zachmongare/Li-Fi-Communication-System/images/results/effective angle test.jpg

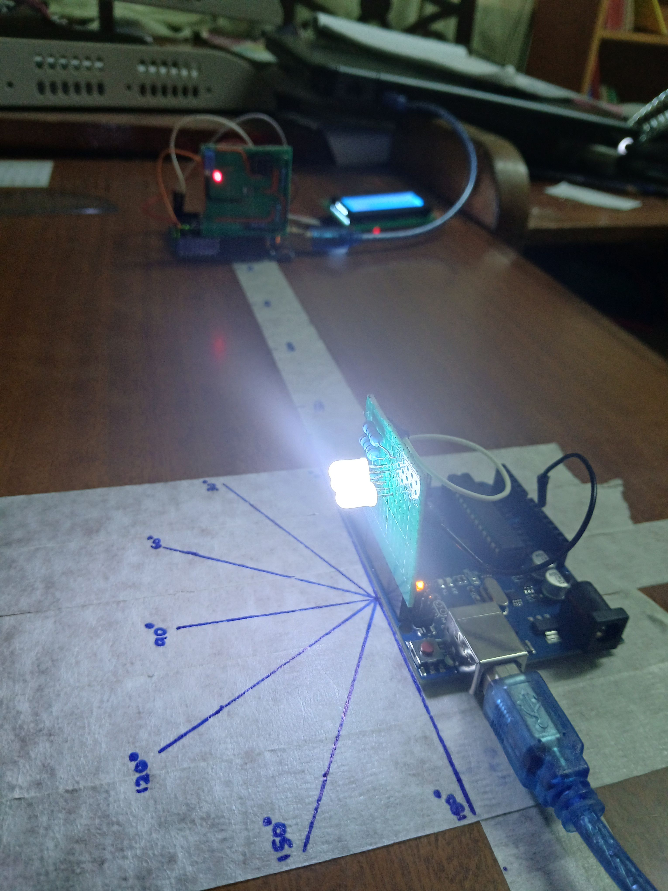
images/results/effective angle test.jpg
