zachmongare/Li-Fi-Communication-System/images/results/range and angle test.jpg

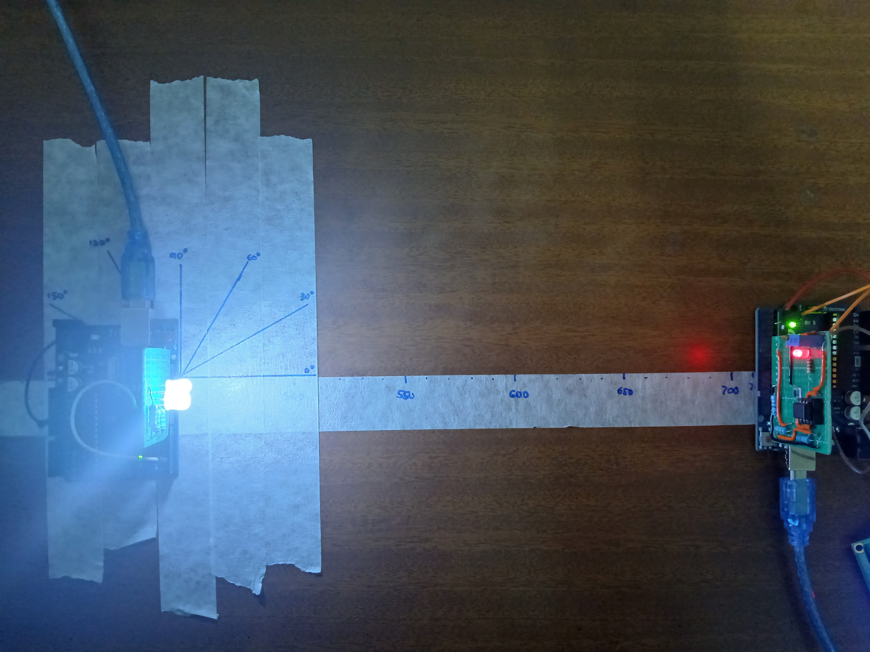
images/results/range and angle test.jpg
