zachmongare/Li-Fi-Communication-System/schematics/receiver_schematic.kicad_sch

## KiCad design schematics/receiver_schematic.kicad_sch (2025-07-15)

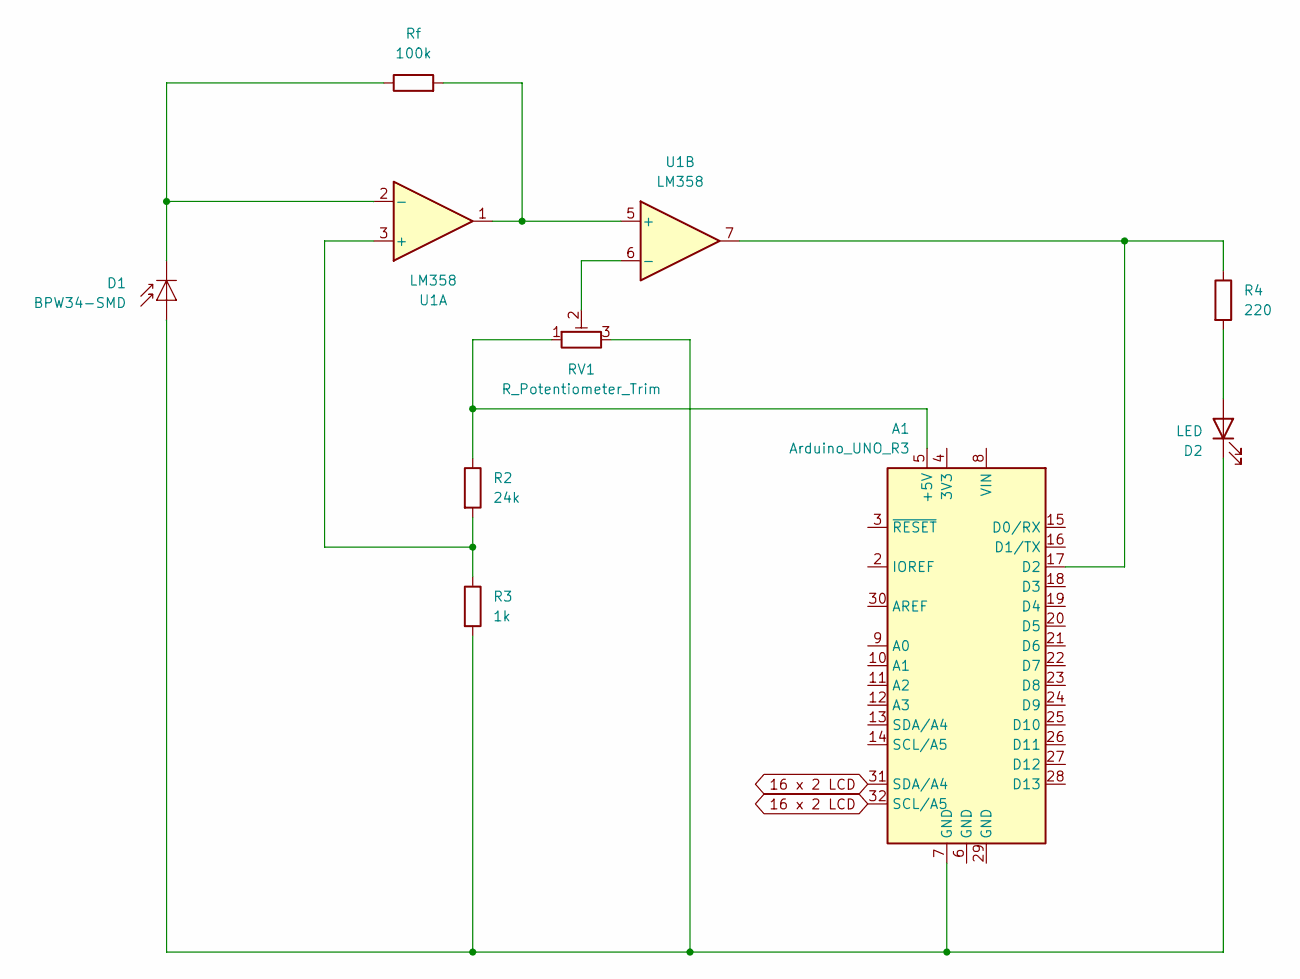
[picture p7: schematic receiver_schematic.kicad_sch]

Parts:
A1: Arduino_UNO_R3
D1: BPW34-SMD; Osram_BPW34S-SMD
D2: LED
R2: 24k
R3: 1k
R4: 220
RV1: R_Potentiometer_Trim
Rf: 100k
U1: LM358

Connections:
unnamed: A1.5 (+5V), R2.1, RV1.1
unnamed: A1.7 (GND), D1.2 (A), D2.1 (K), R3.2, RV1.3
unnamed: A1.17 (D2), R4.1, U1.7
unnamed: D1.1 (K), Rf.1, U1.2 (-)
unnamed: D2.2 (A), R4.2
unnamed: R2.2, R3.1, U1.3 (+)
unnamed: RV1.2, U1.6 (-)
unnamed: Rf.2, U1.1, U1.5 (+)
x 2 LCD: A1.31 (SDA/A4), A1.32 (SCL/A5)
