zachmongare/Li-Fi-Communication-System/schematics/transmitter_schematic.kicad_sch

## KiCad design schematics/transmitter_schematic.kicad_sch (2025-07-15)

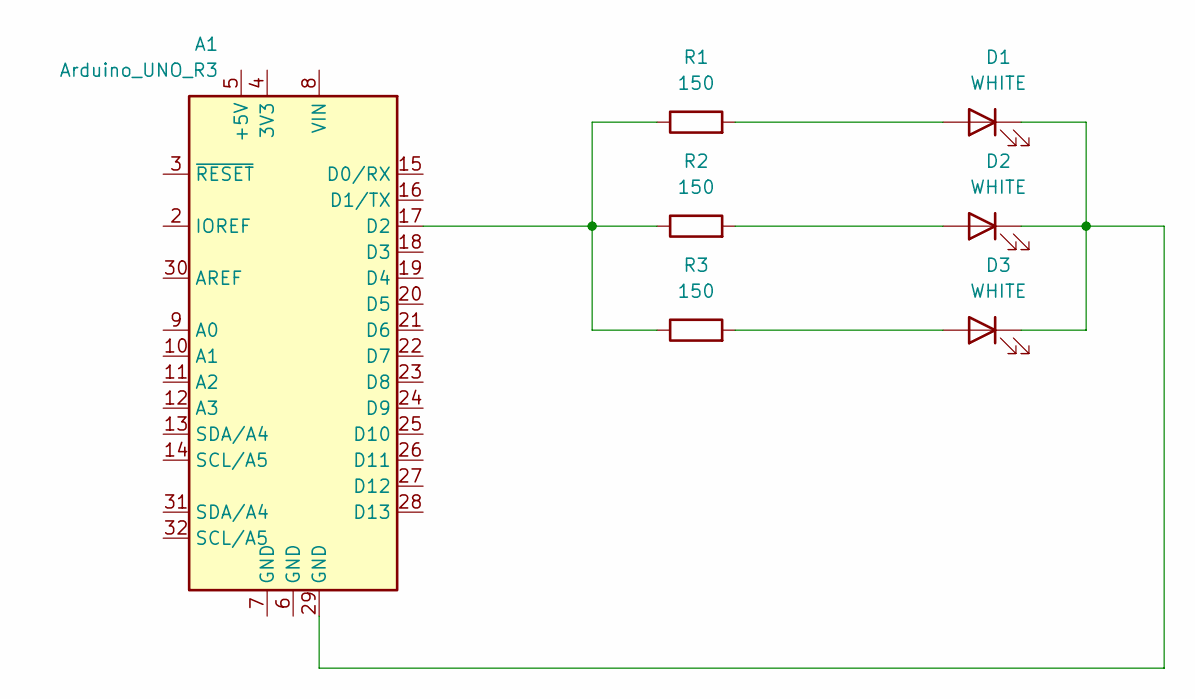
[picture p8: schematic transmitter_schematic.kicad_sch]

Parts:
A1: Arduino_UNO_R3
D1, D2, D3: WHITE
R1, R2, R3: 150

Connections:
unnamed: A1.17 (D2), R1.1, R2.1, R3.1
unnamed: A1.29 (GND), D1.1 (K), D2.1 (K), D3.1 (K)
unnamed: D1.2 (A), R1.2
unnamed: D2.2 (A), R2.2
unnamed: D3.2 (A), R3.2
