zachmongare/Li-Fi-Communication-System/images/results/effective range test.jpg

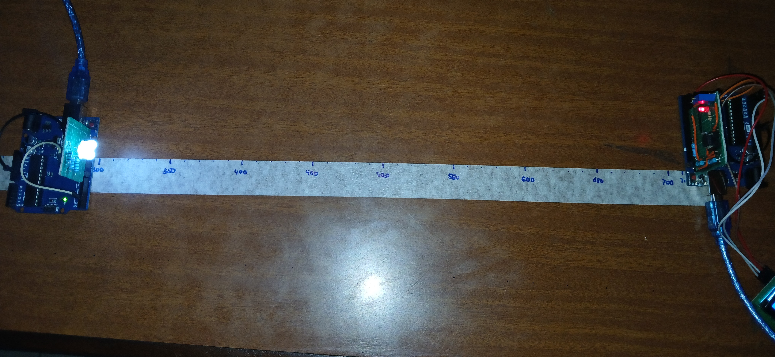
images/results/effective range test.jpg
