zachmongare/Li-Fi-Communication-System/images/results/received message 1.jpg

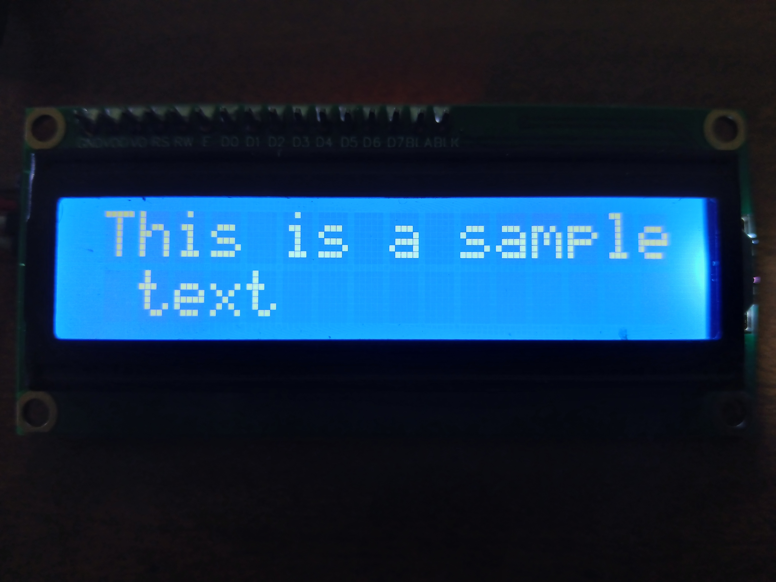
images/results/received message 1.jpg
