zachmongare/Li-Fi-Communication-System/images/results/received message 2.jpg

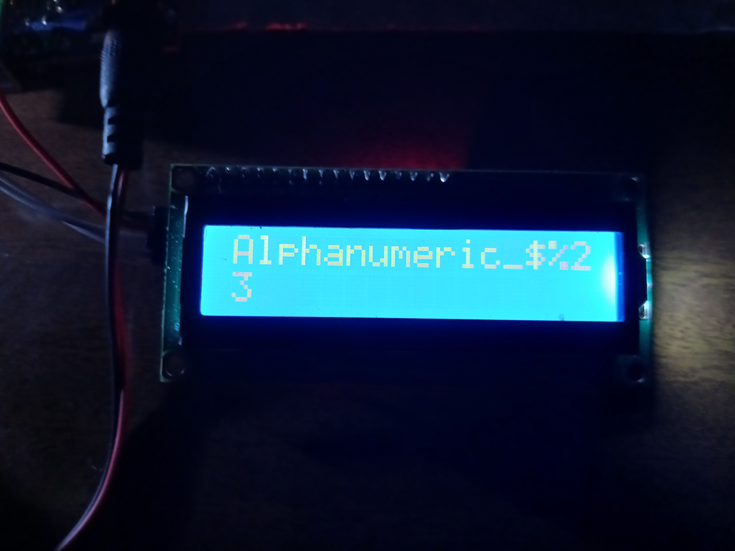
images/results/received message 2.jpg
