zachmongare/Li-Fi-Communication-System/images/results/received message 3.jpg

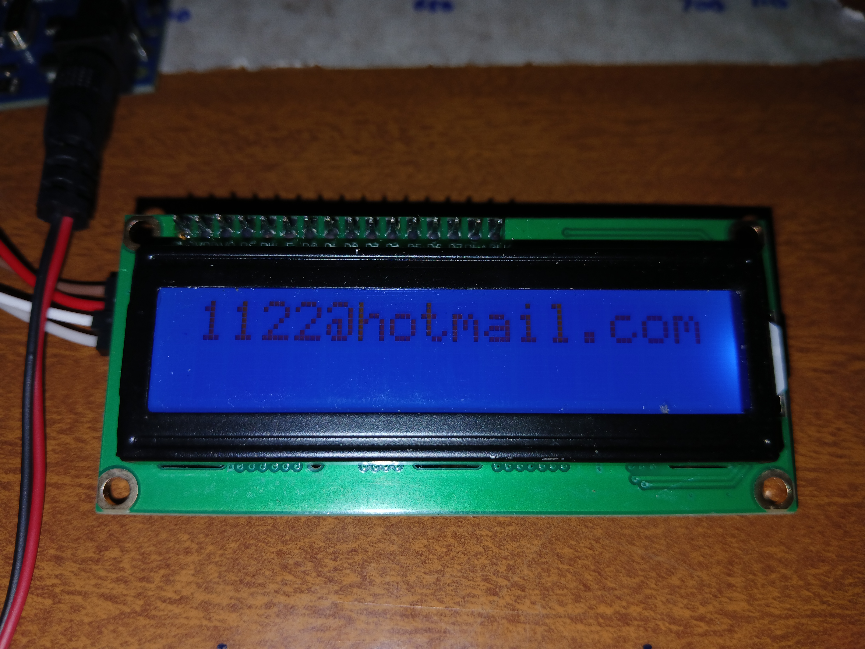
images/results/received message 3.jpg
