zachmongare/Li-Fi-Communication-System/images/results/sent message 1.png

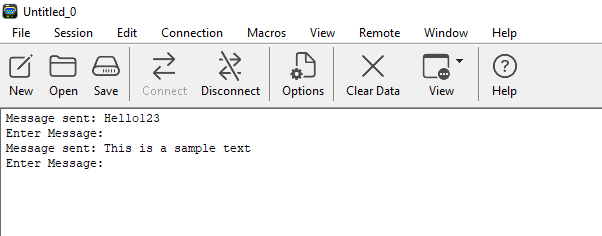
images/results/sent message 1.png
