zachmongare/Li-Fi-Communication-System/images/results/sent message 2.png

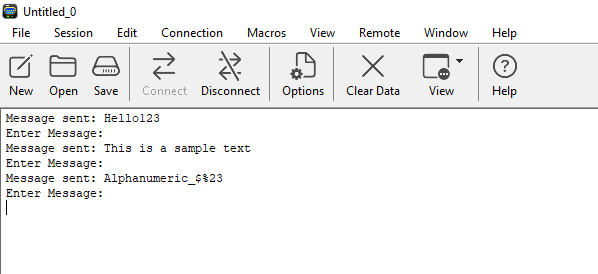
images/results/sent message 2.png
