zachmongare/Li-Fi-Communication-System/images/results/sent message 3.png

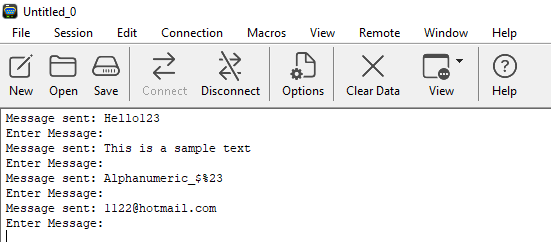
images/results/sent message 3.png
